Kleptobot/bike_telemetry/3D_CAD/OBike rev4.png

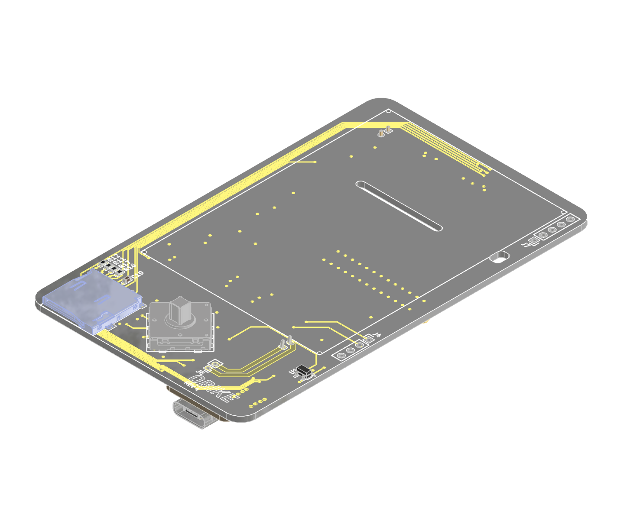
3D_CAD/OBike rev4.png
