Kleptobot/bike_telemetry/src/HAL/SensorData.hpp

#ifndef SENSORDATA_H
#define SENSORDATA_H

struct imu_data {
    float f32_acc_x;
    float f32_acc_y;
    float f32_acc_z;
    float f32_gyro_x;
    float f32_gyro_y;
    float f32_gyro_z;
};

struct dps_data {
    float f32_DSP_Pa;
    float f32_DSP_Temp;
    bool dpsValid;
    float f32_RTC_Temp;
};

struct location_data {
    bool valid;
    double longitude;
    double latitude;
};

struct data_record { 
    float value;
    bool live;
};

inline bool operator!=(const location_data& lhs, const location_data& rhs) {
    return lhs.valid != rhs.valid || lhs.longitude != rhs.longitude || lhs.latitude != rhs.latitude;
}

#endif /* SENSORDATA_H */
