Kleptobot/bike_telemetry/src/HAL/Bluetooth/csc.cpp

#include <iterator>
#include "csc.hpp"

std::vector<csc*> csc::_cscDevices;

void csc::csc_notify_callback(BLEClientCharacteristic* chr, uint8_t* data, uint16_t len) {
  //itterate the members of the bt device base
  for (csc* dev : _cscDevices) {
    //compare the conn handle of the evt with the conn handle of the device servic (static cast to a csc, safe because we know the type)
    if (chr->connHandle() == dev->csc_serv.connHandle()) {
      //call the underlying notify method for the instance (again static cast)
      dev->csc_notify(chr, data, len);
      return;
    }
  }
}

void csc::begin() {
  // Initialize csc client
  csc_serv.begin();

  // Initialize client characteristics of csc.
  // Note: Client Char will be added to the last service that is begin()ed.
  csc_loc.begin();
  csc_feat.begin();

  // set up callback for receiving measurement
  csc_meas.setNotifyCallback(csc_notify_callback);
  csc_meas.begin();

  bat_serv.begin();

  bat_meas.setNotifyCallback(bat_notify_callback);
  bat_meas.begin();

  b_cadence_present =0;
  b_speed_present =0;

  _begun = true;
  return;
};

void csc::discover(uint16_t conn_handle) {
  // If csc is not found, disconnect and return
  if (csc_serv.discover(conn_handle) )
  {
    _conn_handle = conn_handle;
    Serial.println("Found CSC");

    if ( !csc_meas.discover() )
    {
      // Measurement chr is mandatory, if it is not found (valid), then disconnect
      return;
    }

    if ( csc_feat.discover() )
    {
      // Read 8-bit BSLC value from peripheral
      
      u32_WheelCount_Prev = 0;
      u16_SpeedEvt_Prev = 0;
      u16_CrankCount_Prev = 0;
      u16_CrankEvt_Prev = 0;
      //f32_kph_raw = 0;
      raw_wheel_rpm = 0;
      f32_cadence_raw = 0;
      f32_wheel_rpm = 0;
      f32_cadence = 0;

      u8_feature = csc_feat.read8();
      b_speed_present = ((u8_feature & 0x01) == 1);
      b_cadence_present = ((u8_feature & 0x02) == 2);
    }
    
    if ( csc_loc.discover() )
    {
      // Read 8-bit BSLC value from peripheral
      u8_location = csc_loc.read8();
    }

    // Reaching here means we are ready to go, let's enable notification on measurement chr
    if ( csc_meas.enableNotify() )
    {
      Serial.println("Ready to receive CSC Measurement value");
    }else{
      Serial.println("Couldn't enable notify for CSC Measurement");
    }
    if(bat_serv.discover(conn_handle))
    {
      Serial.println("Found bat");
      
      if (bat_meas.discover() )
      {
        u8_Batt = bat_meas.read8();
        //Serial.print("Batt: "); Serial.println(u8_batt);
      }
      if ( bat_meas.enableNotify() )
      {
        Serial.println("Ready to receive BAT Measurement value");
      }else
      {
        Serial.println("Couldn't enable notify for BAT Measurement");
      }
    }
  }else{
    Bluefruit.disconnect(conn_handle);
    Serial.println("Found NONE");
  }
  return;
}

bool csc::discovered() {
  return csc_meas.discovered();
}

void csc::csc_notify(BLEClientCharacteristic* chr, uint8_t* data, uint16_t len) {
  // https://github.com/oesmith/gatt-xml/blob/master/org.bluetooth.service.cycling_speed_and_cadence.xml
  
  uint8_t offset = 1;
  uint32_t u32_WheelCount;
  uint16_t u16_SpeedEvt, u16_CrankCount, u16_CrankEvt;

  // The payload comes from the remote sensor, so every field must be bounds
  // checked against len before it is read. A short or malformed notification
  // previously read past the end of the buffer.
  if (len < 1) return;

  if ((data[0] & 0x01) ==1) {
    if (len < offset + 6u) return;      // uint32 revolutions + uint16 event time
    memcpy(&u32_WheelCount, data+offset, 4);
    offset += 4;
    memcpy(&u16_SpeedEvt, data+offset, 2);
    offset += 2;

    //check for disconnect
    if(_disconnected) {
      u16_SpeedEvt_Prev=u16_SpeedEvt;
      u32_WheelCount_Prev=u32_WheelCount;
      _wheelResync = true;
      _disconnected=false;
    }
  
    //check for overflow of speed evt
    if (u16_SpeedEvt != u16_SpeedEvt_Prev) {
      // Free-running uint16 counter: plain unsigned subtraction already wraps
      // correctly, and does so without the off-by-one of (65535 - prev).
      u16_speed_delta = (uint16_t)(u16_SpeedEvt - u16_SpeedEvt_Prev);
      u16_SpeedEvt_Prev = u16_SpeedEvt;
      millis_at_spd_evt = millis();
      exp_next_spd_evt = millis_at_spd_evt + uint(u16_speed_delta*0.9765625); //convert 1/1024ths of a second into milliseconds
    }

    u16_SpeedEvt_Last = u16_SpeedEvt;

    //free-running uint32 counter, wraps correctly under subtraction
    u32_WheelCount_delta = (uint32_t)(u32_WheelCount - u32_WheelCount_Prev);
    u32_WheelCount_Prev = u32_WheelCount;

    // The cumulative total only advances on genuine deltas: the first packet
    // after construction/discover/reconnect baselines Prev instead of adding
    // the sensor's whole lifetime count to the total.
    if (_wheelResync) {
      _wheelResync = false;
    } else {
      u32_WheelCount_Total += u32_WheelCount_delta;
    }

    //calculate the rate of change and convert to km/h
    raw_wheel_rpm = 0;
    if (u16_speed_delta > 0) {
      //speed delta is in 1024ths of a second, 3.6 * 1024/1000 = 3.6864
      //f32_kph_raw = f32_circ * 3.6864 *float(u32_WheelCount_delta)/float(u16_speed_delta);

      //csc time delta is in 1/1024ths of a second
      //
      raw_wheel_rpm = 61440.0 * float(u32_WheelCount_delta)/float(u16_speed_delta);
    }
  }
  if ((data[0] & 0x02) == 2) {
    if (len < offset + 4u) return;      // uint16 revolutions + uint16 event time
    memcpy(&u16_CrankCount, data+offset, 2);
    offset += 2;
    memcpy(&u16_CrankEvt, data+offset, 2);
    offset += 2;

    //check for disconnect
    if(_disconnected) {
      u16_CrankEvt_Prev = u16_CrankEvt;
      u16_CrankCount_Prev = u16_CrankCount;
      _crankResync = true;
      _disconnected=false;
    }

    //check for overflow of crank evt
    if (u16_CrankEvt != u16_CrankEvt_Prev) {
      u16_crank_delta = (uint16_t)(u16_CrankEvt - u16_CrankEvt_Prev);
      millis_at_cad_evt = millis();
      exp_next_cad_evt = millis_at_cad_evt + uint(u16_crank_delta*0.9765625); //convert 1/1024ths of a second into milliseconds
      u16_CrankEvt_Prev = u16_CrankEvt;
    }

    u16_CrankEvt_Last = u16_CrankEvt;

    //free-running uint16 counter, wraps correctly under subtraction
    u16_CrankCount_delta = (uint16_t)(u16_CrankCount - u16_CrankCount_Prev);
    u16_CrankCount_Prev = u16_CrankCount;

    if (_crankResync) {
      _crankResync = false;
    } else {
      u32_CrankCount_Total += u16_CrankCount_delta;
    }
    
    //calculate rate of change and convert to rpm
    f32_cadence_raw = 0;
    if (u16_crank_delta>0) {
      //61440 is 60*1024: converts the crank delta and 1/1024s time delta into revolutions per minute
      f32_cadence_raw = 61440.0 *float(u16_CrankCount_delta)/float(u16_crank_delta);
    }
  }
}

data_record csc::getSpeed() {
  // Average over the devices that actually contribute, not over every CSC
  // device present. Dividing by _cscDevices.size() halved the reading when
  // one of two sensors reported cadence only.
  data_record speed = {0, false};
  uint16_t contributors = 0;
  for (csc* dev : _cscDevices) {
    if(dev->b_speed_present) {
      speed.value += dev->f32_wheel_rpm;
      speed.live = true;
      contributors++;
    }
  }
  if (contributors > 0) {
    speed.value /= contributors;
  }
  return speed;
}

data_record csc::getCadence() {
  data_record cadence = {0, false};
  uint16_t contributors = 0;
  for (csc* dev : _cscDevices) {
    if(dev->b_cadence_present) {
      cadence.value += dev->f32_cadence;
      cadence.live = true;
      contributors++;
    }
  }
  if (contributors > 0) {
    cadence.value /= contributors;
  }
  return cadence;
}

const csc* csc::latestWheelSource() {
  const csc* best = nullptr;
  for (const csc* dev : _cscDevices) {
    if (!dev->b_speed_present) continue;
    if (!best || dev->wheelEvtMillis() > best->wheelEvtMillis()) best = dev;
  }
  return best;
}

const csc* csc::latestCrankSource() {
  const csc* best = nullptr;
  for (const csc* dev : _cscDevices) {
    if (!dev->b_cadence_present) continue;
    if (!best || dev->crankEvtMillis() > best->crankEvtMillis()) best = dev;
  }
  return best;
}

void csc::disconnect(uint16_t conn_handle, uint8_t reason) {
  (void) conn_handle;
  (void) reason;

  b_speed_present = false;
  b_cadence_present = false;
  Serial.println("CSC Disconnected");

  BT_Device::disconnect(conn_handle,reason);
}

void csc::update(uint32_t now) {
  float est_wheel_rpm = 0, f32_cad_est = 0;
  
  //use the last known u16_CrankCount_delta delta and an adjusted time delta to come up with an actual cadance estimate
  if (now>exp_next_cad_evt) {
    uint32_t diff = now - exp_next_cad_evt;
    uint32_t delta_adjusted = u16_crank_delta + diff * 1.024f; //convert milliseconds into 1/1024ths of a second (1024/1000)
    if ( delta_adjusted > 0)
      f32_cad_est = 61440.0 *float(u16_CrankCount_delta)/float(delta_adjusted);
  }else{
    f32_cad_est = f32_cadence_raw;
  }
  
  //low pass filter the cadance estimate
  f32_cadence = f32_cad_est * 0.01 + f32_cadence * 0.99;

  //use the last known wheelcount delta and an adjusted time delta to come up with an actual speed estimate
  if(now>exp_next_spd_evt) {
    uint32_t diff = now - exp_next_spd_evt;
    uint32_t delta_adjusted = u16_speed_delta + diff * 1.024f; //milliseconds into 1/1024ths of a second
    if ( delta_adjusted > 0)
      est_wheel_rpm = 61440.0 * float(u32_WheelCount_delta)/float(delta_adjusted);
  }else{
    est_wheel_rpm = raw_wheel_rpm;
  }
  
  //low pass filter the speed estimate
  f32_wheel_rpm = est_wheel_rpm * 0.01 + f32_wheel_rpm * 0.99;
};
