Kleptobot/bike_telemetry/src/HAL/LC76G.hpp

#ifndef LC76G_H
#define LC76G_H

#include <Arduino.h>
#include <Wire.h>
#include <queue>
#include <vector>
#include <TinyGPSPlus.h>
#include "HAL/StorageInterface.hpp"

static const uint8_t MAX_NMEA_LEN = 255;

class LC76G
{
    private:

    struct Sentence {
        char data[MAX_NMEA_LEN];
        uint16_t length;

        Sentence(){}
        Sentence(uint8_t* buff, uint8_t len) {
            memcpy(data, buff, len);
            length = len;
        }
    };

    static int build_no_args(char* buf, uint16_t size, const char* cmd, const void*) {
        return snprintf(buf, size, "%s", cmd);
    }

    static int build_1u8(char* buf, uint16_t size, const char* cmd, const void* payload) {
        const Payload1U8* p = static_cast<const Payload1U8*>(payload);

        return snprintf(buf, size, "%s,%u", cmd, p->a);
    }

    static int build_1char_1u8(char* buf, uint16_t size, const char* cmd, const void* payload) {
        const Payload1Ch1U8* p = static_cast<const Payload1Ch1U8*>(payload);

        return snprintf(buf, size, "%s,%s,%u", cmd, p->a, p->b);
    }

    static int build_1char(char* buf, uint16_t size, const char* cmd, const void* payload) {
        const Payload1Ch* p = static_cast<const Payload1Ch*>(payload);

        return snprintf(buf, size, "%s,%s", cmd, p->a);
    }

    static int build_2u8(char* buf, uint16_t size, const char* cmd, const void* payload) {
        const Payload2U8* p = static_cast<const Payload2U8*>(payload);

        return snprintf(buf, size, "%s,%u,%u", cmd, p->a, p->b);
    }

    static bool decode_none(Sentence response, int& numArgs, void* payload) {
        numArgs = 0;
        return true; 
    }

    // Acknowledgement of the form "$PAIR001,<cmd>,<result>*CS" -- the value we
    // want is the third field. Skips the talker and the echoed command id.
    // Scans into unsigned int rather than using the %hh length modifier, which
    // newlib-nano's reduced scanf does not reliably support.
    static bool decode_1u8(Sentence response, int& numArgs, void* payload) {
        uint8_t* byte_array = (uint8_t*)payload;
        unsigned int a = 0;
        numArgs = sscanf(response.data,"%*[^,],%*[^,],%u",&a);
        if (numArgs != 1) return false;
        byte_array[0] = (uint8_t)a;
        return true;
    }

    // Query reply of the form "$PAIR063,<type>,<rate>*CS" -- two numeric fields
    // after the talker.
    static bool decode_2u8(Sentence response, int& numArgs, void* payload) {
        uint8_t* byte_array = (uint8_t*)payload;
        unsigned int a = 0, b = 0;
        numArgs = sscanf(response.data,"%*[^,],%u,%u",&a,&b);
        if (numArgs != 2) return false;
        byte_array[0] = (uint8_t)a;
        byte_array[1] = (uint8_t)b;
        return true;
    }

    // %[^,] rather than %s: the fields are comma-separated, and %s would run
    // past the delimiter and swallow the rest of the sentence.
    static bool decode_1char_1u8(Sentence response, int& numArgs, void* payload) {
      Payload1Ch1U8* p = (Payload1Ch1U8*)payload;
      unsigned int b = 0;
      numArgs = sscanf(response.data, "%*[^,],%9[^,],%u", p->a, &b);
      if (numArgs != 2) return false;
      p->b = (uint8_t)b;
      return true;
    }


    public:
    LC76G(IStorage& storage) 
    : _state(STATE_IDLE),
    _state_prev(STATE_IDLE),
    _mode(MODE_RECEIVE),
    _stateEntry(millis()),
    _lastI2cAction(millis()),
    _wire(nullptr),
    _storage(storage),
    _rxLength(0),
    _transactionLength(0) {}

    //enum of all avaialble commands
    enum CmdId : int16_t {
        PAIR_LOW_POWER_ENTRY_RTC_MODE,
        GET_NMEA_MSG_RATE,
        SET_NMEA_MSG_RATE,
        GET_NAVIGATION_MODE,
        SET_NAVIGATION_MODE,
        GET_STATIC_THRESHOLD,
        SET_STATIC_THRESHOLD,
        RESTORE_DEFAULT_SETTING,
        GET_GLP_STATUS,
        GLP_ENABLE,
        GNSS_SUBSYS_HOT_START,
        GNSS_SUBSYS_WARM_START,
        GNSS_SUBSYS_COLD_START,
        SET_NMEA_RATE,
        GET_NMEA_RATE,
        SAVE_TO_NVRAM
    };

    struct CommandDef {
        CmdId             cmdId;    // logical ID

        const char* cmd;            // command body to send
        int (*build)(               // builder to use for this command
            char* outBuf,
            uint16_t outSize,
            const char* cmd,
            const void* payload
        );                            

        const char* response;       // response body for matching against
        bool (*decode)(             // decoder to use for this response
            Sentence resp,
            int& numArgs,
            void* payload         
        );
        uint32_t          timeoutMs;  
    };

    inline static const CommandDef COMMANDS[] = {
        {PAIR_LOW_POWER_ENTRY_RTC_MODE, "PAIR650", &build_no_args, nullptr, nullptr, 200 },
        {GET_NMEA_MSG_RATE, "PAIR063", &build_1u8, "$PAIR063", &decode_2u8, 90000 },
        {SET_NMEA_MSG_RATE, "PAIR062", &build_2u8, "PAIR001,062", &decode_1u8, 90000 },
        {GET_NAVIGATION_MODE, "PAIR081", &build_no_args, "$PAIR081", &decode_1u8, 90000 },
        {SET_NAVIGATION_MODE, "PAIR080", &build_1u8, "$PAIR001,080", &decode_none, 90000 },
        {GET_STATIC_THRESHOLD, "PAIR071", &build_no_args, "$PAIR071", &decode_1u8, 90000 },
        {SET_STATIC_THRESHOLD, "PAIR070", &build_1u8, "$PAIR001,070", &decode_none, 90000 },
        {RESTORE_DEFAULT_SETTING, "PAIR514", &build_no_args, nullptr, nullptr, 200 },
        {GET_GLP_STATUS, "PAIR681", &build_no_args, "$PAIR681", &decode_1u8, 90000 },
        {GLP_ENABLE, "PAIR680", &build_1u8, "PAIR001,680", &decode_none, 90000 },
        {GNSS_SUBSYS_HOT_START, "PAIR004", &build_no_args, nullptr, nullptr, 200 },
        {GNSS_SUBSYS_WARM_START, "PAIR005", &build_no_args, nullptr, nullptr, 200 },
        {GNSS_SUBSYS_COLD_START, "PAIR006", &build_no_args, nullptr, nullptr, 200 },
        {SET_NMEA_RATE, "PQTMCFGMSGRATE,W", &build_1char_1u8, nullptr, nullptr, 10000 },
        {GET_NMEA_RATE, "PQTMCFGMSGRATE,R", &build_1char, "$PQTMCFGMSGRATE,OK", nullptr, 10000 },
        {SAVE_TO_NVRAM, "PAIR511", &build_no_args, "PAIR001,511,1", nullptr, 10000 }

    };

    using ResponseCallback = void (*)(int numArgs, const void* payload, void* userContext);

    // Unified state machine
    enum State {
        STATE_IDLE,
        STATE_STEP1A_SEND,
        STATE_STEP1A_DELAY,
        STATE_STEP1B_READ,
        STATE_STEP1B_DELAY,
        STATE_STEP2A_SEND,
        STATE_STEP2A_DELAY,
        STATE_STEP2B_TRANSACT,
        STATE_PROCESS_RECEIVE,
        STATE_COMPLETE_RECEIVE,
        STATE_COMPLETE_TRANSMIT,
        STATE_ERROR
    };

    struct PendingResponse {
        CmdId commandId;
        ResponseCallback callback;
        void* userContext;
        uint32_t sendTimeMs;
        uint32_t timeoutMs;
    };

    struct Payload1U8 {
        uint8_t a;
    };

    struct Payload2U8 {
        uint8_t a;
        uint8_t b;
    };

    struct Payload1Ch1U8 {
        char a[10];
        uint8_t b;
    };

    struct Payload1Ch {
        char a[10];
    };
    
    // Initialize the GPS module
    bool begin(TwoWire* wire = &Wire);
    
    // Non-blocking update
    void update();

    // main state machine
    State stateMachine();

    // Get received data (only valid after STATUS_SUCCESS from receive)
    uint16_t getReceivedData(uint8_t* buffer, uint16_t maxLength);
    
    // Queue a command to send (non-blocking)
    bool queueCommand(const uint8_t* data, uint16_t length);
    
    // Check if I2C bus is busy
    bool isBusy() const { return (_state != STATE_IDLE) && (_state != STATE_ERROR); }

    // --- I2C bus instrumentation (consumed by HAL's per-second summary) ------
    // Monotonic raw counters: HAL computes the deltas, so there is no reset
    // call to get wrong. dbgMaxDrainGapMs is the worst-case wait between
    // completed buffer drains -- the number the sensor sampling budget has to
    // keep bounded, or the module's internal buffer backs up and NMEA
    // corrupts (the empirical "faster sensors broke the GPS" failure).
    uint32_t dbgTxCount()       const { return _dbgTxCount; }      // every Wire read/write
    uint32_t dbgDrainCycles()   const { return _dbgDrainCycles; }  // buffer reads with len > 0
    uint32_t dbgBytesDrained()  const { return _dbgBytesDrained; }
    uint32_t dbgZeroLenPolls()  const { return _dbgZeroLenPolls; }   // probes that found nothing
    uint32_t dbgMaxDrainGapMs() const { return _dbgMaxDrainGapMs; }
    uint8_t  dbgErrorCount()    const { return _errorCount; }

    // Milliseconds since the state machine last STARTED a bus cycle (any
    // cycle, including a zero-length probe). Feeds the arbiter's backpressure
    // rule (see HAL/I2CArbiter.hpp): starts are the signal that the GNSS is
    // getting its turns, independent of whether the module currently has
    // data to drain. 0 = no cycle yet this power cycle.
    uint32_t msSinceLastCycleStart() const {
        return _lastCycleStartMs == 0 ? 0 : millis() - _lastCycleStartMs;
    }

    //tell class that another device just performed i2c
    void i2c_wait() {_lastI2cAction = millis();};
    void sendCommand(CmdId cmdId, ResponseCallback cb, void* userCtx, const void* payload);

    TinyGPSPlus& gps() { return _gps; };
    const TinyGPSPlus& gps() const { return _gps; };
    void closeDataFile() {
        dataFile.flush();
        dataFile.close();
        delay(50);
    }

    private:
    // I2C addresses
    static const uint8_t ADDR_CR_OR_CW = 0x50;
    static const uint8_t ADDR_READ = 0x54;
    static const uint8_t ADDR_WRITE = 0x58;
    
    // Protocol constants
    static const uint16_t CMD_READ = 0xAA51;
    static const uint16_t CMD_WRITE = 0xAA53;
    static const uint8_t CMD_LENGTH = 8;
    
    static const uint16_t REG_TX_LEN = 0x08;
    static const uint16_t REG_TX_BUF = 0x2000;
    static const uint16_t REG_RX_LEN = 0x04;
    static const uint16_t REG_RX_BUF = 0x1000;
    
    // One NMEA read is issued as a single Wire transaction, so MAX_BUFFER is
    // bounded by three things at once:
    //   1. nRF52 TWIM RXD.MAXCNT is an 8-bit register (<= 255).
    //   2. TwoWire::requestFrom returns uint8_t (<= 255).
    //   3. The core DMAs the received bytes into its SERIAL_BUFFER_SIZE
    //      RingBuffer array -- reads beyond that corrupt adjacent RAM. The
    //      build raises it to 256 (platformio.ini), which this must stay under.
    // 128 doubles the drain throughput ceiling (fewer cycles per byte for the
    // same ~50 ms cycle cost) while staying well inside all three bounds.
    static const uint16_t MAX_BUFFER = 128;
    static_assert(MAX_BUFFER <= 255,
                  "TWIM RXD.MAXCNT is 8-bit and requestFrom() returns uint8_t");

    static const uint8_t i2c_DELAY = 10;

    struct TxCommand {
        std::vector<uint8_t> data;
        TxCommand(const uint8_t* buf, uint16_t len) : data(buf, buf + len) {}
    };
    
    // Operation mode
    enum Mode {
        MODE_RECEIVE,
        MODE_TRANSMIT
    };
  
    State _state, _state_prev;
    Mode _mode;
    unsigned long _stateEntry, _lastI2cAction;
    TwoWire* _wire;
    
    TinyGPSPlus _gps;
    IStorage& _storage;
    File32 dataFile;
    
    // Buffers
    uint8_t _rxBuffer[MAX_BUFFER];
    uint16_t _rxLength;
    uint8_t _txBuffer[MAX_BUFFER];
    uint8_t _NMEAbuffer[MAX_NMEA_LEN];
    uint16_t _NMEAlength;
    uint16_t _txLength;
    std::queue<TxCommand> _txQueue;
    std::queue<Sentence> _sentences;
    std::vector<PendingResponse> _responses;
    
    uint8_t _lengthBytes[4];
    uint8_t _cmdBuffer[CMD_LENGTH];
    uint16_t _transactionLength;
    uint8_t _errorCount = 0;

    // Bus instrumentation accumulators (see the dbg* getters above).
    uint32_t _dbgTxCount = 0, _dbgDrainCycles = 0, _dbgBytesDrained = 0;
    uint32_t _dbgZeroLenPolls = 0, _dbgMaxDrainGapMs = 0, _lastDrainOkMs = 0;
    uint32_t _lastCycleStartMs = 0;   // arbiter backpressure signal (see above)

    bool _CR = false;
    bool _$found = false;
    
    // Helpers
    bool i2cWrite(uint8_t addr, const uint8_t* data, uint16_t length);
    bool i2cRead(uint8_t addr, uint8_t* data, uint16_t length);
    bool sendReadRequest(uint16_t reg, uint16_t length);
    bool sendWriteRequest(uint16_t reg, uint16_t length);
    bool readResponse(uint8_t* buffer, uint16_t length);
    bool writeData(const uint8_t* buffer, uint16_t length);
    int Recovery_I2c();

    // Functions for handling protocol
    uint8_t calculate_xor_checksum(const uint8_t* data, size_t length);
    void addSentence();
    void pollResponseTimeouts();
    void processSentence(Sentence s);

    // Returned by getCommand() when a CmdId has no table entry. Callers must
    // check for it: returning 0 on a miss would silently resolve to
    // COMMANDS[0], which is PAIR_LOW_POWER_ENTRY_RTC_MODE -- i.e. an unknown
    // command would put the receiver to sleep.
    static const uint16_t INVALID_COMMAND = 0xFFFF;

    uint16_t getCommand(CmdId cmdId) const {
        for (uint16_t i =0; i< std::size(COMMANDS); ++i) {
            if ( COMMANDS[i].cmdId == cmdId) return i;
        }
        return INVALID_COMMAND;
    }
};

#endif /* LC76G_H */
