Kleptobot/bike_telemetry/src/HAL/Bluetooth/csc.hpp

#ifndef CSC_H
#define CSC_H

#include <Arduino.h>
#include <vector>
#include <memory>
#include <bluefruit.h>
#include "HAL/SensorData.hpp"

#include "BT_Device.hpp"

// Cycling Speed and Cadence configuration
#define     GATT_CSC_UUID                           0x1816
#define     GATT_CSC_MEASUREMENT_UUID               0x2A5B
#define     GATT_CSC_FEATURE_UUID                   0x2A5C
#define     GATT_SC_CONTROL_POINT_UUID              0x2A55

/* Device Information configuration */
#define     GATT_DEVICE_INFO_UUID                   0x180A
#define     GATT_MANUFACTURER_NAME_UUID             0x2A29
#define     GATT_MODEL_NUMBER_UUID                  0x2A24

/*CSC Measurement flags*/
#define     CSC_MEASUREMENT_WHEEL_REV_PRESENT       0x01
#define     CSC_MEASUREMENT_CRANK_REV_PRESENT       0x02

/* CSC feature flags */
#define     CSC_FEATURE_WHEEL_REV_DATA              0x01
#define     CSC_FEATURE_CRANK_REV_DATA              0x02
#define     CSC_FEATURE_MULTIPLE_SENSOR_LOC         0x04

/* SC Control Point op codes */
#define     SC_CP_OP_SET_CUMULATIVE_VALUE           1
#define     SC_CP_OP_START_SENSOR_CALIBRATION       2
#define     SC_CP_OP_UPDATE_SENSOR_LOCATION         3
#define     SC_CP_OP_REQ_SUPPORTED_SENSOR_LOCATIONS 4
#define     SC_CP_OP_RESPONSE                       16

/*SC Control Point response values */
#define     SC_CP_RESPONSE_SUCCESS                  1
#define     SC_CP_RESPONSE_OP_NOT_SUPPORTED         2
#define     SC_CP_RESPONSE_INVALID_PARAM            3
#define     SC_CP_RESPONSE_OP_FAILED                4

class csc : public BT_Device {

  private:
    BLEClientService        csc_serv  = BLEClientService(GATT_CSC_UUID);
    BLEClientCharacteristic csc_meas  = BLEClientCharacteristic(GATT_CSC_MEASUREMENT_UUID);
    BLEClientCharacteristic csc_feat  = BLEClientCharacteristic(GATT_CSC_FEATURE_UUID);
    BLEClientCharacteristic csc_loc   = BLEClientCharacteristic(GATT_SENSOR_LOCATION_UUID);

    static std::vector<csc*> _cscDevices;
    
    static void csc_notify_callback(BLEClientCharacteristic* chr, uint8_t* data, uint16_t len);

    // Body sensor location value is 8 bit
    const char* feat_str[4] = {"other", "Speed", "Cadence", "Speed & Cadence"};
    const float f32_circ = 2127;
    // csc objects are heap-allocated via `new csc(MAC)`, so these get no
    // static zero-init. begin() already zeroed the two presence flags; the
    // rest were left indeterminate.
    uint32_t u32_WheelCount_Prev = 0;
    uint16_t u16_SpeedEvt_Prev = 0, u16_CrankCount_Prev = 0, u16_CrankEvt_Prev = 0;
    uint8_t u8_feature = 0, u8_location = 0;
    uint32_t millis_at_spd_evt = 0, millis_at_cad_evt = 0;
    uint32_t exp_next_spd_evt= 0, exp_next_cad_evt=0;
    uint32_t u32_WheelCount_delta = 0;
    uint16_t u16_CrankCount_delta = 0, u16_speed_delta = 0, u16_crank_delta = 0;

    // Cumulative revolution totals and last-received native event times,
    // maintained for the measurement frame (see HAL/Measurements.hpp).
    // Bookkeeping only -- no existing behaviour reads them. In-class
    // initialisers: csc objects are heap-allocated (see comment above).
    uint32_t u32_WheelCount_Total = 0, u32_CrankCount_Total = 0;
    uint16_t u16_SpeedEvt_Last = 0, u16_CrankEvt_Last = 0;
    // True until the first packet after construction/discover/reconnect has
    // baselined the Prev counters, so the sensor's whole lifetime count is
    // not injected into the totals.
    bool _wheelResync = true, _crankResync = true;
    
    csc(){
      this->bt_type = E_Type_BT_Device::bt_csc;
    }

    void removeFromLocalList() override {
      _cscDevices.erase(
        std::remove(_cscDevices.begin(), _cscDevices.end(), this),
        _cscDevices.end()
      );
    }

  protected:
    csc(MacAddress MAC){
      this->bt_type = E_Type_BT_Device::bt_csc;
      this->MAC=MAC;
      this->begin();
    }

  public:
    bool b_speed_present = false, b_cadence_present = false;
    float raw_wheel_rpm = 0.0f, f32_wheel_rpm = 0.0f;
    float f32_cadence_raw = 0.0f, f32_cadence = 0.0f;
    virtual ~csc(){};
    
    static void create_csc(MacAddress MAC)
    {
      btDevices.push_back(std::unique_ptr<csc>(new csc(MAC)));
      _cscDevices.push_back(static_cast<csc*>(btDevices.back().get()));
    };


    static data_record getSpeed();
    static data_record getCadence();

    // --- Measurement-frame surface (see HAL/Measurements.hpp) ----------------
    uint32_t wheelRevTotal() const { return u32_WheelCount_Total; }
    uint32_t crankRevTotal() const { return u32_CrankCount_Total; }
    uint16_t lastWheelEvt1024() const { return u16_SpeedEvt_Last; }
    uint16_t lastCrankEvt1024() const { return u16_CrankEvt_Last; }
    uint32_t wheelEvtMillis() const { return millis_at_spd_evt; }
    uint32_t crankEvtMillis() const { return millis_at_cad_evt; }

    // The speed/cadence-capable device whose most recent event is freshest --
    // the natural "primary" when several CSC sensors are connected. Returns
    // nullptr when none has ever reported.
    static const csc* latestWheelSource();
    static const csc* latestCrankSource();

    void begin();

    void discover(uint16_t conn_handle);

    void csc_notify(BLEClientCharacteristic* chr, uint8_t* data, uint16_t len);
    
    bool discovered() override;

    void disconnect(uint16_t conn_handle, uint8_t reason) override;

    void update(uint32_t now) override;
};

 #endif /* CSC_H */
