Kleptobot/bike_telemetry/src/HAL/Bluetooth/BT_Device.hpp

#ifndef BT_DEVICE_H
#define BT_DEVICE_H

#include <Arduino.h>
#include <vector>
#include <memory>
#include <bluefruit.h>
#include <functional>
#include <algorithm> 

#include "HAL/BluetoothInterface.hpp"
#include "MAC.hpp"
#include "DebugConfig.hpp"

#define     GATT_BAT_UUID                           0x180F
#define     GATT_BAT_MEASUREMENT_UUID               0x2A19
#define     GATT_SENSOR_LOCATION_UUID               0x2A5D

/* Sensor location enum */
#define     SENSOR_LOCATION_OTHER                   0
#define     SENSOR_LOCATION_TOP_OF_SHOE             1
#define     SENSOR_LOCATION_IN_SHOE                 2
#define     SENSOR_LOCATION_HIP                     3
#define     SENSOR_LOCATION_FRONT_WHEEL             4
#define     SENSOR_LOCATION_LEFT_CRANK              5
#define     SENSOR_LOCATION_RIGHT_CRANK             6
#define     SENSOR_LOCATION_LEFT_PEDAL              7
#define     SENSOR_LOCATION_RIGHT_PEDAL             8
#define     SENSOR_LOCATION_FROT_HUB                9
#define     SENSOR_LOCATION_REAR_DROPOUT            10
#define     SENSOR_LOCATION_CHAINSTAY               11
#define     SENSOR_LOCATION_REAR_WHEEL              12
#define     SENSOR_LOCATION_REAR_HUB                13
#define     SENSOR_LOCATION_CHEST                   14
#define     SENSOR_LOCATION_SPIDER                  15
#define     SENSOR_LOCATION_CHAIN_RING              16

class BT_Device {
  public:
    using DeviceDisconnectedCallback = std::function<void(MacAddress MAC)>;

  private:
    static DeviceDisconnectedCallback _onUnexpectedDisconnect;

  protected:
    BLEClientService        bat_serv  = BLEClientService(GATT_BAT_UUID);
    BLEClientCharacteristic bat_meas  = BLEClientCharacteristic(GATT_BAT_MEASUREMENT_UUID);
    
    MacAddress MAC;
    uint8_t u8_Batt = 100;
    // Derived devices are heap-allocated, so these need explicit initialisers.
    // _disconnected in particular is read as a condition in csc::csc_notify
    // before anything assigns it.
    bool _begun = false;
    uint16_t _conn_handle = BLE_CONN_HANDLE_INVALID;
    E_Type_BT_Device bt_type = E_Type_BT_Device::bt_csc;
    static std::vector<std::unique_ptr<BT_Device>> btDevices;
    bool _disconnected = false;

    BT_Device(){};
    virtual void removeFromLocalList() {};

  public:
    virtual ~BT_Device() {};
    
    static BT_Device* getDeviceWithMAC(MacAddress MAC);

    static void removeDeviceWithMAC(MacAddress MAC);

    static void removeDevice(std::unique_ptr<BT_Device> device);

    static void disconnect_callback(uint16_t conn_handle, uint8_t reason);

    static void onUnexpectedDisconnect(DeviceDisconnectedCallback cb) { _onUnexpectedDisconnect = cb; }
    
    static void bat_notify_callback(BLEClientCharacteristic* chr, uint8_t* data, uint16_t len);

    static bool all_devices_discovered();

    static bool deviceWithMacDiscovered(MacAddress MAC);

    void bat_notify(BLEClientCharacteristic* chr, uint8_t* data, uint16_t len);

    virtual void update(uint32_t now) {};

    MacAddress getMac() {return MAC;}
    E_Type_BT_Device getType() const {return bt_type;}
    bool begun() const {return _begun;}
    bool disconnected() const {return _disconnected;}
    uint8_t readBatt() const {return u8_Batt;}
    uint16_t getConnHandle(){return _conn_handle;};
    
    virtual void discover(uint16_t conn_handle) {};
    virtual bool discovered() { return false; };

    virtual void disconnect(uint8_t reason);
    virtual void disconnect(uint16_t conn_handle, uint8_t reason);

    virtual void begin() {};
};

 #endif /* BT_DEVICE_H */
