Kleptobot/bike_telemetry/src/Loggers/ILogger.hpp

#ifndef LOGGERINTERFACE_H
#define LOGGERINTERFACE_H

#include "DataModel/DataModel.hpp"
#include <vector>

// FIT and TCX both want speed in m/s; the telemetry pipeline works in km/h.
inline double kmhToMs(double kmh) { return kmh / 3.6; }

// Exactly what a trackpoint logger needs, and nothing else. Replaces the old
// Telemetry struct in the ILogger surface -- the raw imu/dps blocks it also
// carried were consumed by nobody. Field names match the old Telemetry ones
// the logger bodies reference, so only the signatures changed.
struct Trackpoint {
    double latitude  = 0.0;   // degrees
    double longitude = 0.0;   // degrees
    float altitude   = 0.0f;  // metres
    float speed      = 0.0f;  // km/h
    float heartrate  = 0.0f;  // bpm
    float power      = 0.0f;  // watts (power meter, or est-power if no meter)
    float cadence    = 0.0f;  // rpm
    float distance   = 0.0f;  // metres (cumulative at this point)
    // Fitness channels (from FitnessFusion; ride-scoped cumulative where noted)
    float calories          = 0.0f;  // kcal accumulated this ride
    float normalizedPower   = 0.0f;  // 30 s rolling NP (power meter), watts (0 if no meter)
    float intensityFactor   = 0.0f;  // NP / FTP (0 if FTP unset)
    float tss               = 0.0f;  // accumulated training stress score
    uint8_t hrZone          = 0;     // current HR zone 1-5 (0 = no HR)
    uint8_t powerZone       = 0;     // current power zone 1-5 (0 = no power/FTP)
};

struct Lap {
  timeData startTime;
  float maxHRM;
  float totalHRM;
  float totalCadence;
  float maxSpeed;
        float totalDistance = 0;     // Cumulative distance in meters
  uint16_t parts = 0;
  // Fitness accumulators (cumulative-from-last-trackpoint for the lap)
  float totalCalories = 0.0f;        // cumulative kcal from FitnessFusion
  float totalTss = 0.0f;             // cumulative TSS from FitnessFusion
  float lastNormalizedPower = 0.0f;   // last NP value seen (watts)
  float lastIntensityFactor = 0.0f;  // last IF value seen
};

class ILogger {
public:
    // Timer-time support: pause() shifts every time anchor forward by the
    // time actually spent logging since the last resume/start, so all
    // wall-clock subtraction (elapsed_Total, elapsed_Lap, and every duration
    // written to file) always yields timer time with pauses excluded.
    void pause(const timeData& currentTime) {
        timeDuration d = currentTime - _pauseAnchor;
        _startTime = _startTime + d;
        for (auto& l : laps) l.startTime = l.startTime + d;
    }
    void resume(const timeData& currentTime) { _pauseAnchor = currentTime; }

    virtual void startLogging(const timeData& currentTime) =0 ;
    virtual void addTrackpoint(const Trackpoint& tp, const timeData& currentTime) = 0;
    virtual void newLap(const timeData& currentTime) = 0;
    virtual bool finaliseLogging() = 0;
    virtual const timeDuration elapsed_Total() const = 0;
    virtual const timeDuration elapsed_Lap() const = 0;
 
    // Not part of ILogger, but kept for parity with the original TCX logger's
    // public surface in case call sites use these directly.
    const String elapsedString_Total() const {
        timeDuration ts = elapsed_Total();
        return String(ts.hours()) + ":" + String(ts.minutes()) + ":" + String(ts.seconds());
    }
    const String elapsedString_Lap() const {
        timeDuration ts = elapsed_Lap();
        return String(ts.hours()) + ":" + String(ts.minutes()) + ":" + String(ts.seconds());
    }
    
    virtual ~ILogger() = default;
protected:
    // Shared by all loggers: activity anchors + last trackpoint time, in
    // the base so pause()/resume() can shift them for timer-time.
    timeData _startTime;
    timeData _currentTime;
    timeData _pauseAnchor;  // wall time when logging last became active
    std::vector<Lap> laps; // kept public to match original's `laps.back()` usage
};

#endif /* LOGGERINTERFACE_H */
