Kleptobot/bike_telemetry/src/AppEvents.hpp

#ifndef APPEVENTS_H
#define APPEVENTS_H

#include <Arduino.h>
#include <variant>
#include "HAL/BluetoothInterface.hpp"
#include "DataModel/TimeDataProvider.hpp"

enum class AppEventType {
    None,
    SaveTime,
    SaveBiometrics,
    SaveLayout,
    StartLogging,
    StopLogging,
    PauseLogging,
    ResumeLogging,
    NewLap,
    FactoryReset,
    ConnectBluetooth,
    DisconnectBluetooth,
    DiscoverBluetooth,
    ScanBluetooth,
    RestoreDefaultsGPS,
    ResetGPS,
    saveGPSNVRAM,
    setGPSNMEARate,
    UnmountSD,
    Sleep,
    SaveBikeStats
};

struct NMEArateChange {
    int type;
    int rate;
};

struct AppEvent {
    AppEventType type;
    std::variant<int,float,BluetoothDevice,timeData,NMEArateChange> payload;
};

#endif /* APPEVENTS_H */
