Kleptobot/bike_telemetry/src/HAL/button.cpp

#include "button.hpp"
#include "DebugConfig.hpp"

void button::process()
{
    //get current time, millis is good enough for timing button presses
    uint32_t current_time = millis();

    //reset an calculated values
    _short = false;

    //check for rising falling
    _RE = _state && !_state_prev;
    _FE = !_state && _state_prev;

    //capture time of rising edge
    if (_RE) {
        _RETime = current_time;
        if (ENABLE_INPUTS_DEBUG) {
            Serial.println("[Button] Rising edge detected. RETime: " + String(_RETime));
        }
    }

    //capture time of falling edge
    if (_FE) {
        _FETime = current_time;
        if (ENABLE_INPUTS_DEBUG) {
            Serial.println("[Button] Falling edge detected. FETime: " + String(_FETime));
            Serial.println("[Button] Button released. Held time: " + String(_heldTime));
        }
    }

    //based on state and captured edge times calculate the time held/released
    //also check if a short press has been performed
    if (_state) {
        _heldTime = current_time - _RETime;
        _releaseTime = 0;
        if (ENABLE_INPUTS_DEBUG) {
            Serial.println("[Button] Button held. Held time: " + String(_heldTime));
        }
    } else {
        if (_heldTime>_nShortPressTime)
            _short = true;
        _heldTime = 0;
        _releaseTime = current_time - _FETime;
    }

    _long_RE = _heldTime > _nHeldPressTime && !_long;
    _long = _heldTime > _nHeldPressTime;

    _state_prev = _state;
};
