Kleptobot/bike_telemetry/src/HAL/button.hpp

#ifndef BUTTON_H
#define BUTTON_H

#include <Arduino.h>
#include "InputInterface.hpp"

class button
{
    private:
    bool& _state;
    bool _state_prev;
    bool _RE, _FE;
    bool _long, _short;
    uint32_t _RETime = 0, _FETime = 0;
    uint32_t _heldTime = 0;
    uint32_t _releaseTime = 0;
    bool _long_RE;
    static const uint16_t _nHeldPressTime = 1500;
    static const uint16_t _nShortPressTime = 50;

    public:
    button(bool& state) :
        _state(state),
        _state_prev(state),
        _RE(false),
        _FE(false),
        _long(false),
        _short(false),
        _heldTime(0),
        _releaseTime(0),
        _long_RE(false) {}

    void process();

    const buttonState state() const {
        return {_state,_RE,_FE,_short,_long_RE,_heldTime,_releaseTime};
    }
};

#endif /* BUTTON_H */
