Kleptobot/bike_telemetry/src/ui/Widgets/MapWidget.cpp

#include "MapWidget.hpp"
#include <cmath>
#include "Display/Display.hpp"
#include "Map/TileLoader.hpp"
static uint16_t tilePixels[MapWidget::MAP_W * MapWidget::MAP_H];


// ---------------------------------------------------------------------------
// Construction
// ---------------------------------------------------------------------------
MapWidget::MapWidget(int x, int y, int w, int h, DataModel& model)
    : Widget(x, y, w, h), _model(model) {
    // _tilePixels is a plain array member — no heap allocation needed.
    memset(tilePixels, 0, sizeof(tilePixels));
}


// ---------------------------------------------------------------------------
// update() — runs every tick. All SD access is triggered from here.
// render() does zero SD access.
// ---------------------------------------------------------------------------

void MapWidget::update(float dt) {
    // If the widget is not on screen, do nothing. This prevents SD loads
    // when the user is on the telemetry screen.
    if (!visible) return;

    const GpsTrack& track = _model.gpsTrack();
    if (track.version() == _lastVersion) return;
    _lastVersion = track.version();

    const location_data& loc = _model.bus().get<location_data>(Topic::Location);
    if (loc.valid) {
        _centerLat = loc.latitude;
        _centerLon = loc.longitude;
    }

    // Recompute zoom (cheap, only recalculates when _metersPerPixel changes).
    computeZoom();

    // Check whether the set of visible tiles has changed since last load.
    TileKey newKeys[MAX_VISIBLE_TILES];
    int newCount = 0;
    computeVisibleTiles(newKeys, newCount);

    if (_tilesNeedReload || !_tilesCached || visibleTilesChanged(newKeys, newCount)) {
        loadTilesToCache(); // <-- only SD access point in this widget
        memcpy(_cachedTileKeys, newKeys, sizeof(TileKey) * newCount);
        _cachedTileCount = newCount;
        _tilesCached     = true;
        _tilesNeedReload = false;
    }

    _dirty = true;
}

// ---------------------------------------------------------------------------
// render() — no SD access. Composites cached tiles then draws track overlay.
// ---------------------------------------------------------------------------

void MapWidget::render() {
    if (!visible || !_dirty) return;

    // Clear widget area.
    Disp::fillRect(_x, _y, _width, _height, ST77XX_BLACK);

    if (_tilesCached) {
        renderFromCache();
    } else {
        // No tiles loaded yet — show placeholder.
        Disp::drawText(_x + 4, _y + 4, String("No map data"), ST77XX_WHITE);
    }

    // Track overlay is drawn regardless of whether tiles are available,
    // so the breadcrumb trail shows even in the fallback state.
    renderTrack();

    Disp::markDirty(_x, _y, _width, _height);
    _dirty = false;
}

// ---------------------------------------------------------------------------
// computeZoom
// ---------------------------------------------------------------------------

void MapWidget::computeZoom() {
    double latRad = _centerLat * M_PI / 180.0;
    double metersPerPixelAtZoom0 = 156543.03392 * cos(latRad);
    double ideal = metersPerPixelAtZoom0 / _metersPerPixel;
    int zoom = (ideal > 1.0) ? (int)round(log2(ideal)) : 0;
    zoom = max(0, min(19, zoom));
    _currentZoom = zoom;
}

// ---------------------------------------------------------------------------
// computeVisibleTiles
// Determines which (zoom, tx, ty) tiles overlap the current widget viewport.
// ---------------------------------------------------------------------------

void MapWidget::computeVisibleTiles(TileKey* keys, int& count) const {
    count = 0;
    if (_currentZoom < 0) return;

    uint32_t centerTileX, centerTileY;
    TileLoader::latLonToTileXY(_centerLat, _centerLon, _currentZoom, centerTileX, centerTileY);

    int centerPixelXInTile, centerPixelYInTile;
    TileLoader::latLonToTilePixel(_centerLat, _centerLon, _currentZoom, centerPixelXInTile, centerPixelYInTile);

    int64_t globalCenterX = (int64_t)centerTileX * TileLoader::TILE_SIZE + centerPixelXInTile;
    int64_t globalCenterY = (int64_t)centerTileY * TileLoader::TILE_SIZE + centerPixelYInTile;

    int64_t widgetStartX = globalCenterX - MAP_W / 2;
    int64_t widgetStartY = globalCenterY - MAP_H / 2;
    int64_t widgetEndX   = widgetStartX + MAP_W;
    int64_t widgetEndY   = widgetStartY + MAP_H;

    int64_t tileX0 = widgetStartX / TileLoader::TILE_SIZE;
    if (widgetStartX < 0 && (widgetStartX % TileLoader::TILE_SIZE)) --tileX0;
    int64_t tileY0 = widgetStartY / TileLoader::TILE_SIZE;
    if (widgetStartY < 0 && (widgetStartY % TileLoader::TILE_SIZE)) --tileY0;
    int64_t tileX1 = (widgetEndX - 1) / TileLoader::TILE_SIZE;
    int64_t tileY1 = (widgetEndY - 1) / TileLoader::TILE_SIZE;

    for (int64_t ty = tileY0; ty <= tileY1 && count < MAX_VISIBLE_TILES; ++ty) {
        for (int64_t tx = tileX0; tx <= tileX1 && count < MAX_VISIBLE_TILES; ++tx) {
            keys[count++] = { _currentZoom, (uint32_t)tx, (uint32_t)ty };
        }
    }
}

// ---------------------------------------------------------------------------
// visibleTilesChanged
// ---------------------------------------------------------------------------

bool MapWidget::visibleTilesChanged(const TileKey* keys, int count) const {
    if (count != _cachedTileCount) return true;
    for (int i = 0; i < count; ++i) {
        if (!(keys[i] == _cachedTileKeys[i])) return true;
    }
    return false;
}

// ---------------------------------------------------------------------------
// loadTilesToCache
// Reads tile data from SD into _tilePixels. This is the only function in
// MapWidget that performs SD card access.
// ---------------------------------------------------------------------------

void MapWidget::loadTilesToCache() {
    // Clear to black before compositing tiles.
    memset(tilePixels, 0, sizeof(tilePixels));

    if (_currentZoom < 0) return;

    uint32_t centerTileX, centerTileY;
    TileLoader::latLonToTileXY(_centerLat, _centerLon, _currentZoom, centerTileX, centerTileY);

    int centerPixelXInTile, centerPixelYInTile;
    TileLoader::latLonToTilePixel(_centerLat, _centerLon, _currentZoom, centerPixelXInTile, centerPixelYInTile);

    int64_t globalCenterX = (int64_t)centerTileX * TileLoader::TILE_SIZE + centerPixelXInTile;
    int64_t globalCenterY = (int64_t)centerTileY * TileLoader::TILE_SIZE + centerPixelYInTile;

    int64_t widgetStartX = globalCenterX - MAP_W / 2;
    int64_t widgetStartY = globalCenterY - MAP_H / 2;
    int64_t widgetEndX   = widgetStartX + MAP_W;
    int64_t widgetEndY   = widgetStartY + MAP_H;

    int64_t tileX0 = widgetStartX / TileLoader::TILE_SIZE;
    if (widgetStartX < 0 && (widgetStartX % TileLoader::TILE_SIZE)) --tileX0;
    int64_t tileY0 = widgetStartY / TileLoader::TILE_SIZE;
    if (widgetStartY < 0 && (widgetStartY % TileLoader::TILE_SIZE)) --tileY0;
    int64_t tileX1 = (widgetEndX - 1) / TileLoader::TILE_SIZE;
    int64_t tileY1 = (widgetEndY - 1) / TileLoader::TILE_SIZE;

    for (int64_t ty = tileY0; ty <= tileY1; ++ty) {
        for (int64_t tx = tileX0; tx <= tileX1; ++tx) {
            int64_t tileLeft = tx * TileLoader::TILE_SIZE;
            int64_t tileTop  = ty * TileLoader::TILE_SIZE;

            // Region of this tile that overlaps the widget viewport (global coords).
            int64_t copyStartX = max(tileLeft, widgetStartX);
            int64_t copyStartY = max(tileTop,  widgetStartY);
            int64_t copyEndX   = min(tileLeft + TileLoader::TILE_SIZE, widgetEndX);
            int64_t copyEndY   = min(tileTop  + TileLoader::TILE_SIZE, widgetEndY);

            int copyW = (int)(copyEndX - copyStartX);
            int copyH = (int)(copyEndY - copyStartY);
            if (copyW <= 0 || copyH <= 0) continue;

            // Source pixel offset within the tile.
            int srcX = (int)(copyStartX - tileLeft);
            int srcY = (int)(copyStartY - tileTop);

            // Destination offset within _tilePixels.
            int destX = (int)(copyStartX - widgetStartX);
            int destY = (int)(copyStartY - widgetStartY);

            uint32_t tileUx = (uint32_t)tx;
            uint32_t tileUy = (uint32_t)ty;

            if (!TileLoader::tileExists(_currentZoom, tileUx, tileUy)) continue;

            // Load directly into _tilePixels rather than the global canvas.
            TileLoader::loadRawTileToBuffer(
                _currentZoom, tileUx, tileUy,
                tilePixels, MAP_W,   // dest buffer and its stride
                destX, destY,
                srcX, srcY,
                copyW, copyH
            );
        }
    }
}

// ---------------------------------------------------------------------------
// renderFromCache
// Blits _tilePixels into the canvas. No SD access.
// ---------------------------------------------------------------------------

void MapWidget::renderFromCache() {
    uint16_t* canvasBuf = canvas.getBuffer();
    if (!canvasBuf) return;   // GFXcanvas16's malloc can fail and is unchecked

    // Clip to the canvas. This writes straight into the framebuffer rather
    // than going through Adafruit_GFX, so it bypasses the bounds checking in
    // drawPixel -- nothing here was clamping _x/_y, and the widget's position
    // is user-configurable via the display-edit screen. A widget placed with
    // _x > 160 or _y > 240 wrote outside the 153,600-byte allocation.
    const int startX = _x < 0 ? -_x : 0;
    const int startY = _y < 0 ? -_y : 0;
    const int endX   = min(MAP_W, SCREEN_WIDTH  - _x);
    const int endY   = min(MAP_H, SCREEN_HEIGHT - _y);

    if (endX <= startX || endY <= startY) return;   // fully off-screen

    const size_t rowBytes = (size_t)(endX - startX) * sizeof(uint16_t);

    for (int row = startY; row < endY; ++row) {
        const uint16_t* src = tilePixels + row * MAP_W + startX;
        uint16_t* dst = canvasBuf + (_y + row) * SCREEN_WIDTH + (_x + startX);
        memcpy(dst, src, rowBytes);
    }
}

// ---------------------------------------------------------------------------
// renderTrack
// Draws the breadcrumb polyline and current-position dot over the canvas.
// Called after renderFromCache() (or the fallback fill) so it always appears
// on top. No SD access.
// ---------------------------------------------------------------------------

void MapWidget::renderTrack() {
    const auto& track = _model.gpsTrack().points();
    if (track.empty()) {
        if (!_tilesCached) {
            // Nothing to show at all — display a message.
            Disp::drawText(_x + 4, _y + 20, String("No GPS"), ST77XX_WHITE);
        }
        return;
    }

    int px = 0, py = 0;
    bool first = true;
    for (const auto& p : track) {
        int sx, sy;
        project(p.lat, p.lon, sx, sy);

        // Clip to widget bounds before drawing.
        bool inBounds = (sx >= _x && sx < _x + _width && sy >= _y && sy < _y + _height);

        if (!first && inBounds) {
            canvas.drawLine(px, py, sx, sy, ST77XX_GREEN);
        }
        px = sx;
        py = sy;
        first = false;
    }

    // Current position dot.
    const auto& last = track.back();
    int lx, ly;
    project(last.lat, last.lon, lx, ly);
    canvas.fillCircle(lx, ly, 3, ST77XX_RED);
}

// ---------------------------------------------------------------------------
// project
// Equirectangular projection from lat/lon to widget-local pixel coordinates.
// ---------------------------------------------------------------------------

void MapWidget::project(double lat, double lon, int& outX, int& outY) const {
    // Web Mercator, matching the projection the tiles are rendered in.
    //
    // This was previously an equirectangular approximation (flat degrees-to-
    // metres constants) drawn over a Web Mercator raster. The two agree only
    // near the centre of the viewport and only at low latitudes; away from
    // either, the track drifted off the roads beneath it. Projecting both
    // layers the same way removes the class of error rather than tuning it.
    const double n = (double)(1u << _currentZoom);
    const double worldPx = n * (double)TileLoader::TILE_SIZE;

    auto lonToWorldX = [&](double l) {
        return (l + 180.0) / 360.0 * worldPx;
    };
    auto latToWorldY = [&](double l) {
        const double rad = l * M_PI / 180.0;
        return (1.0 - log(tan(rad) + 1.0 / cos(rad)) / M_PI) / 2.0 * worldPx;
    };

    const double cx = _x + (_width  / 2.0);
    const double cy = _y + (_height / 2.0);

    outX = (int)(cx + (lonToWorldX(lon) - lonToWorldX(_centerLon)));
    outY = (int)(cy + (latToWorldY(lat) - latToWorldY(_centerLat)));
}
